DevelBoard/eva/Drawing/shield_display_4.3/shield_display_4.3.PDF

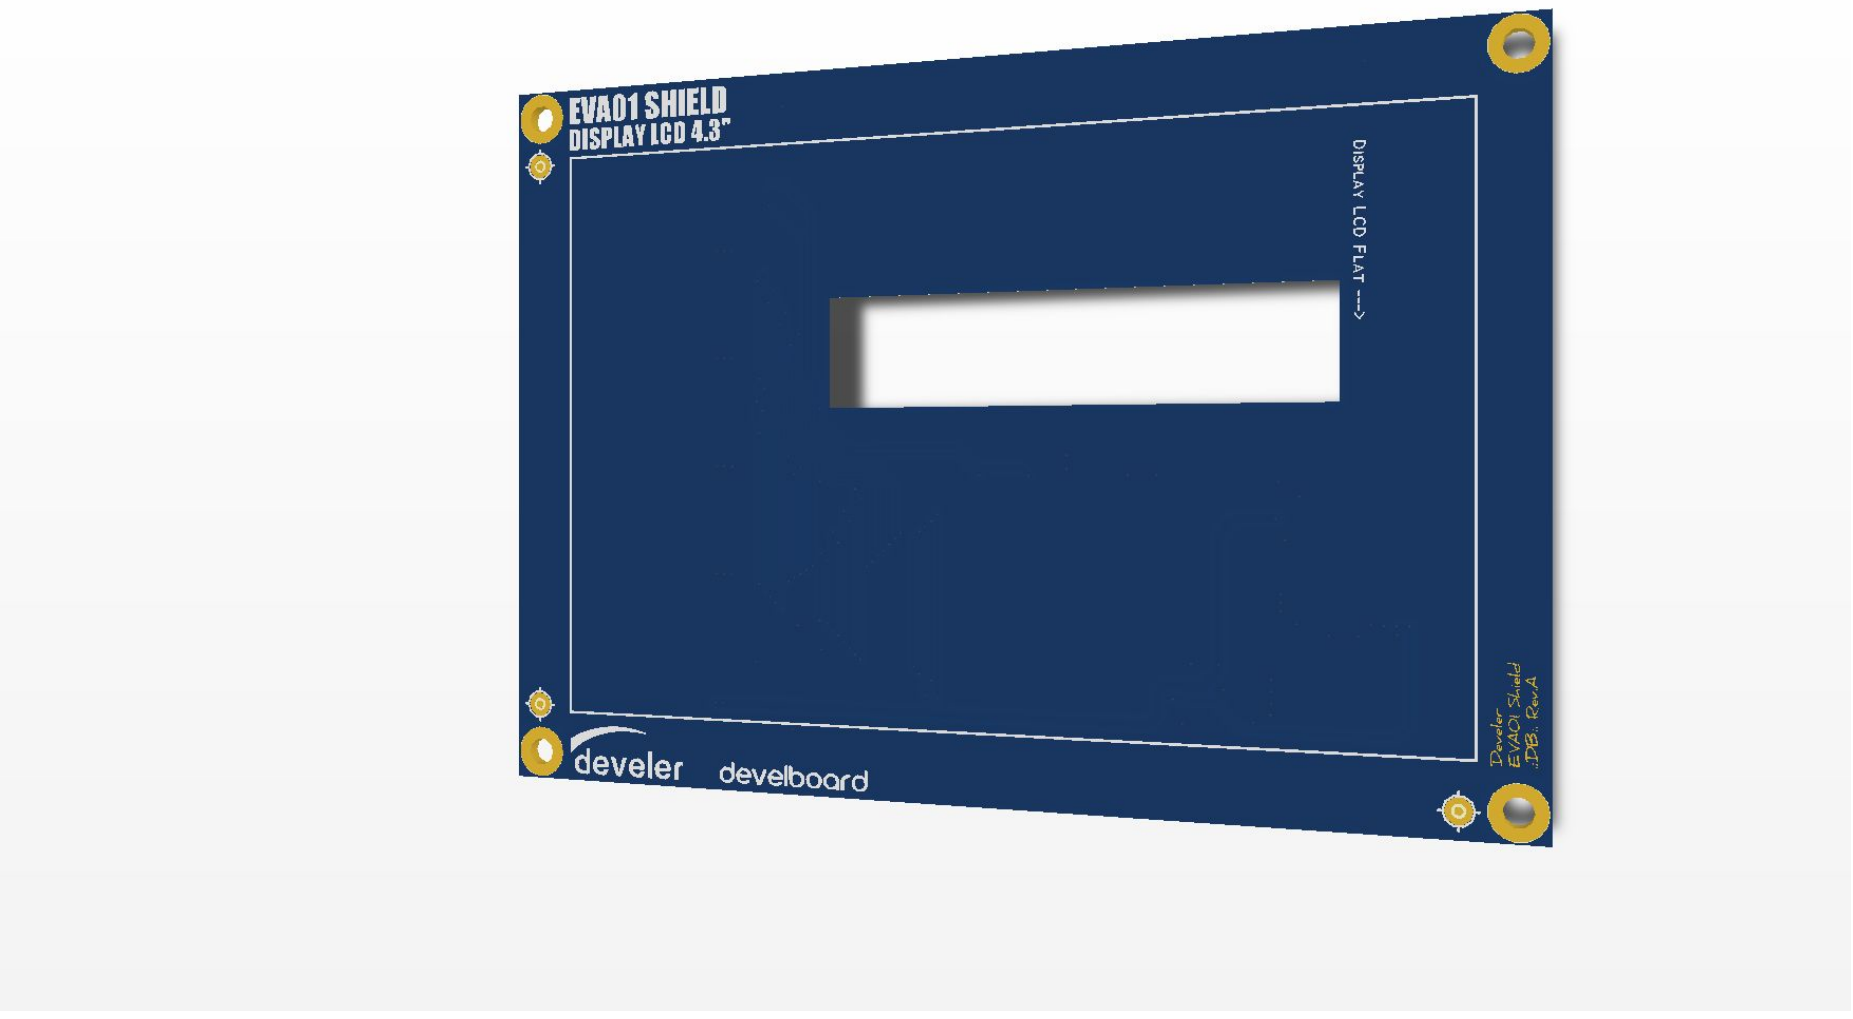
[picture p54: page 1]

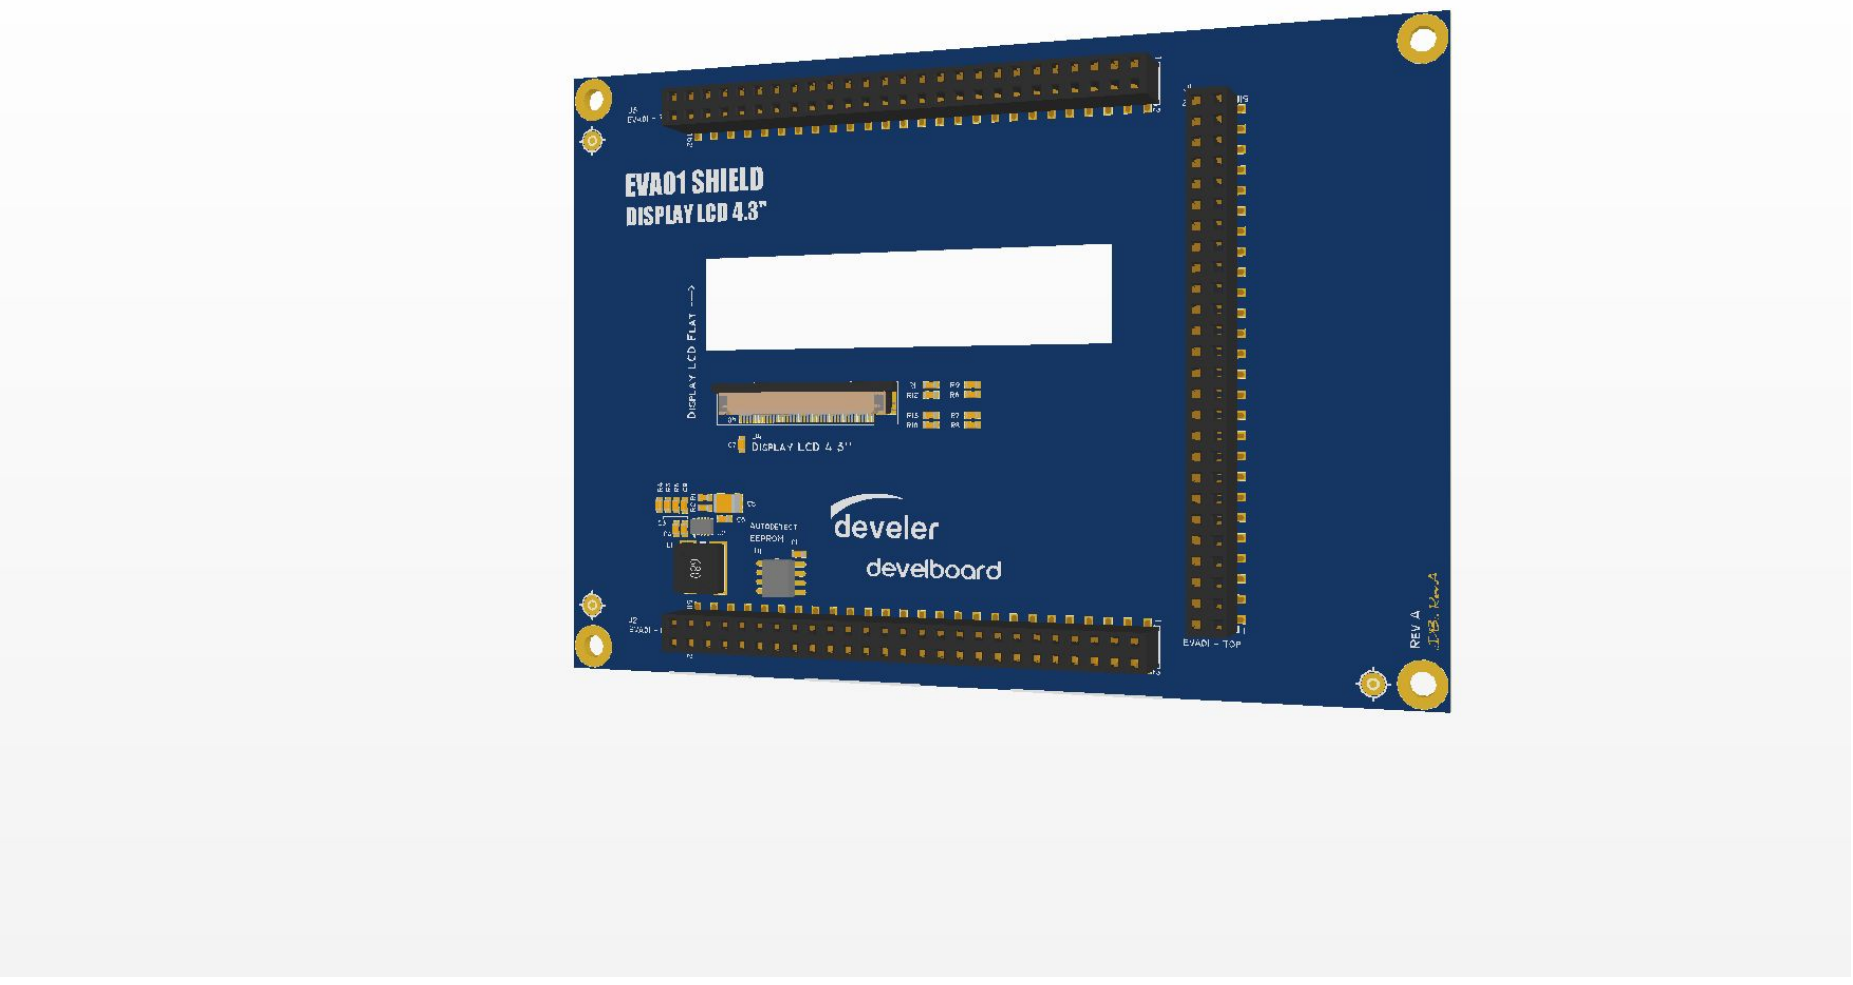
[picture p55: page 2]
