DevelBoard/eva/Drawing/shield_can-display/shield_can-display.PDF

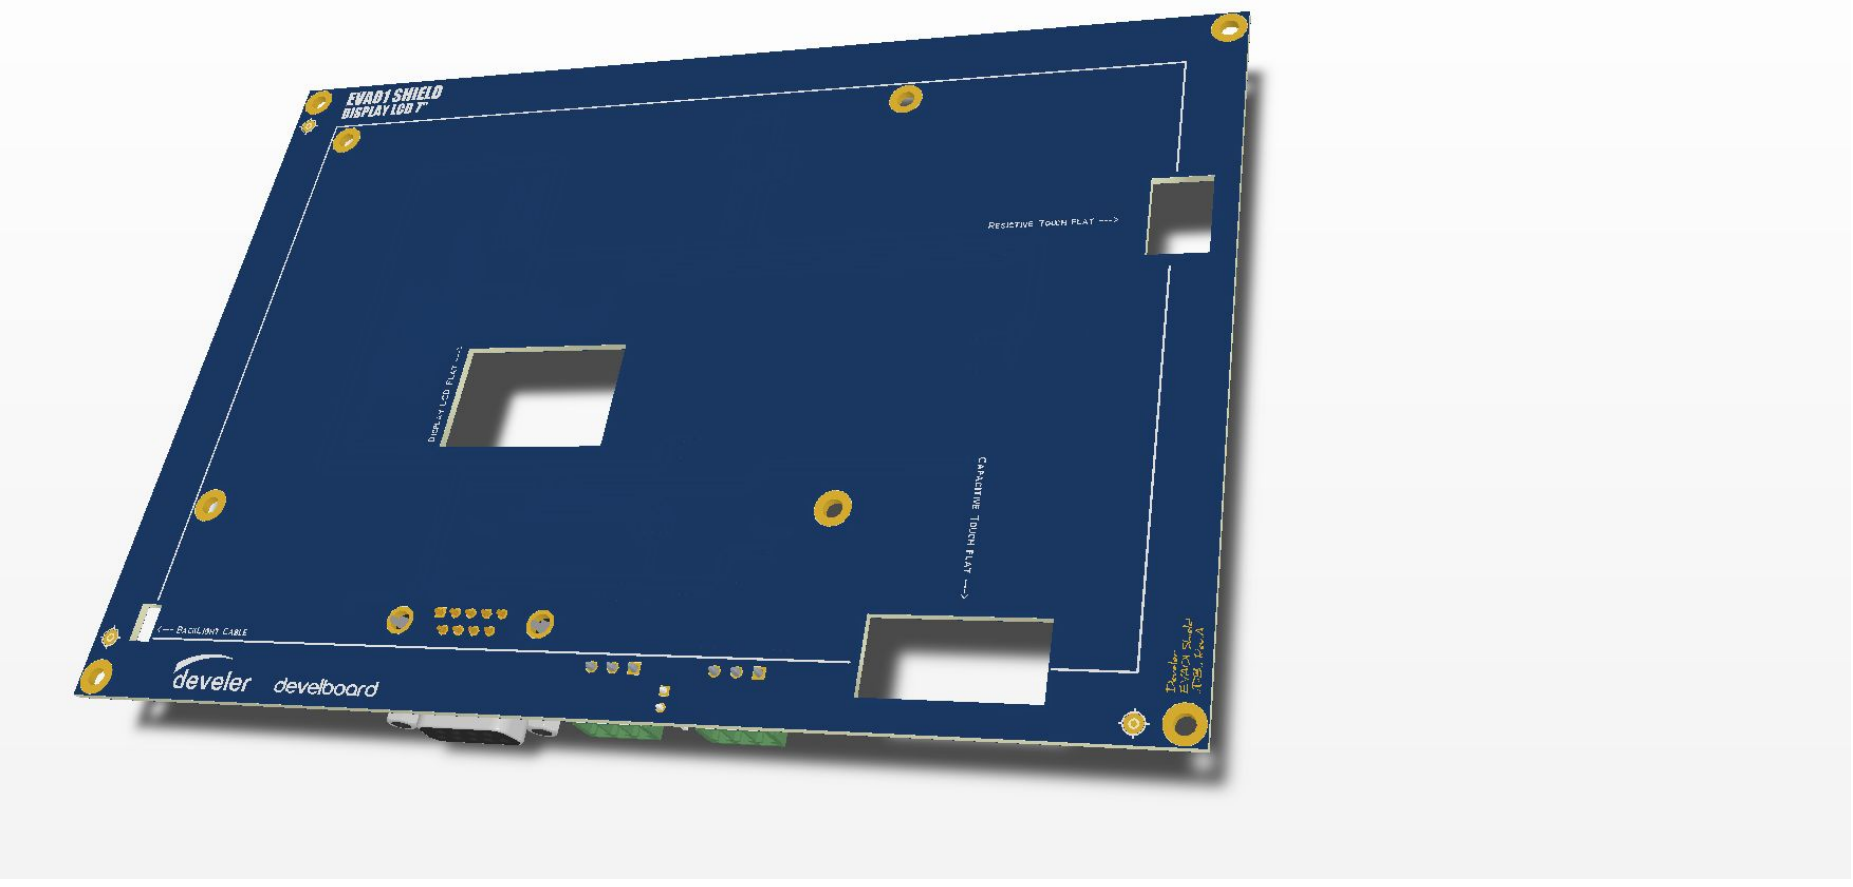
[picture p56: page 1]

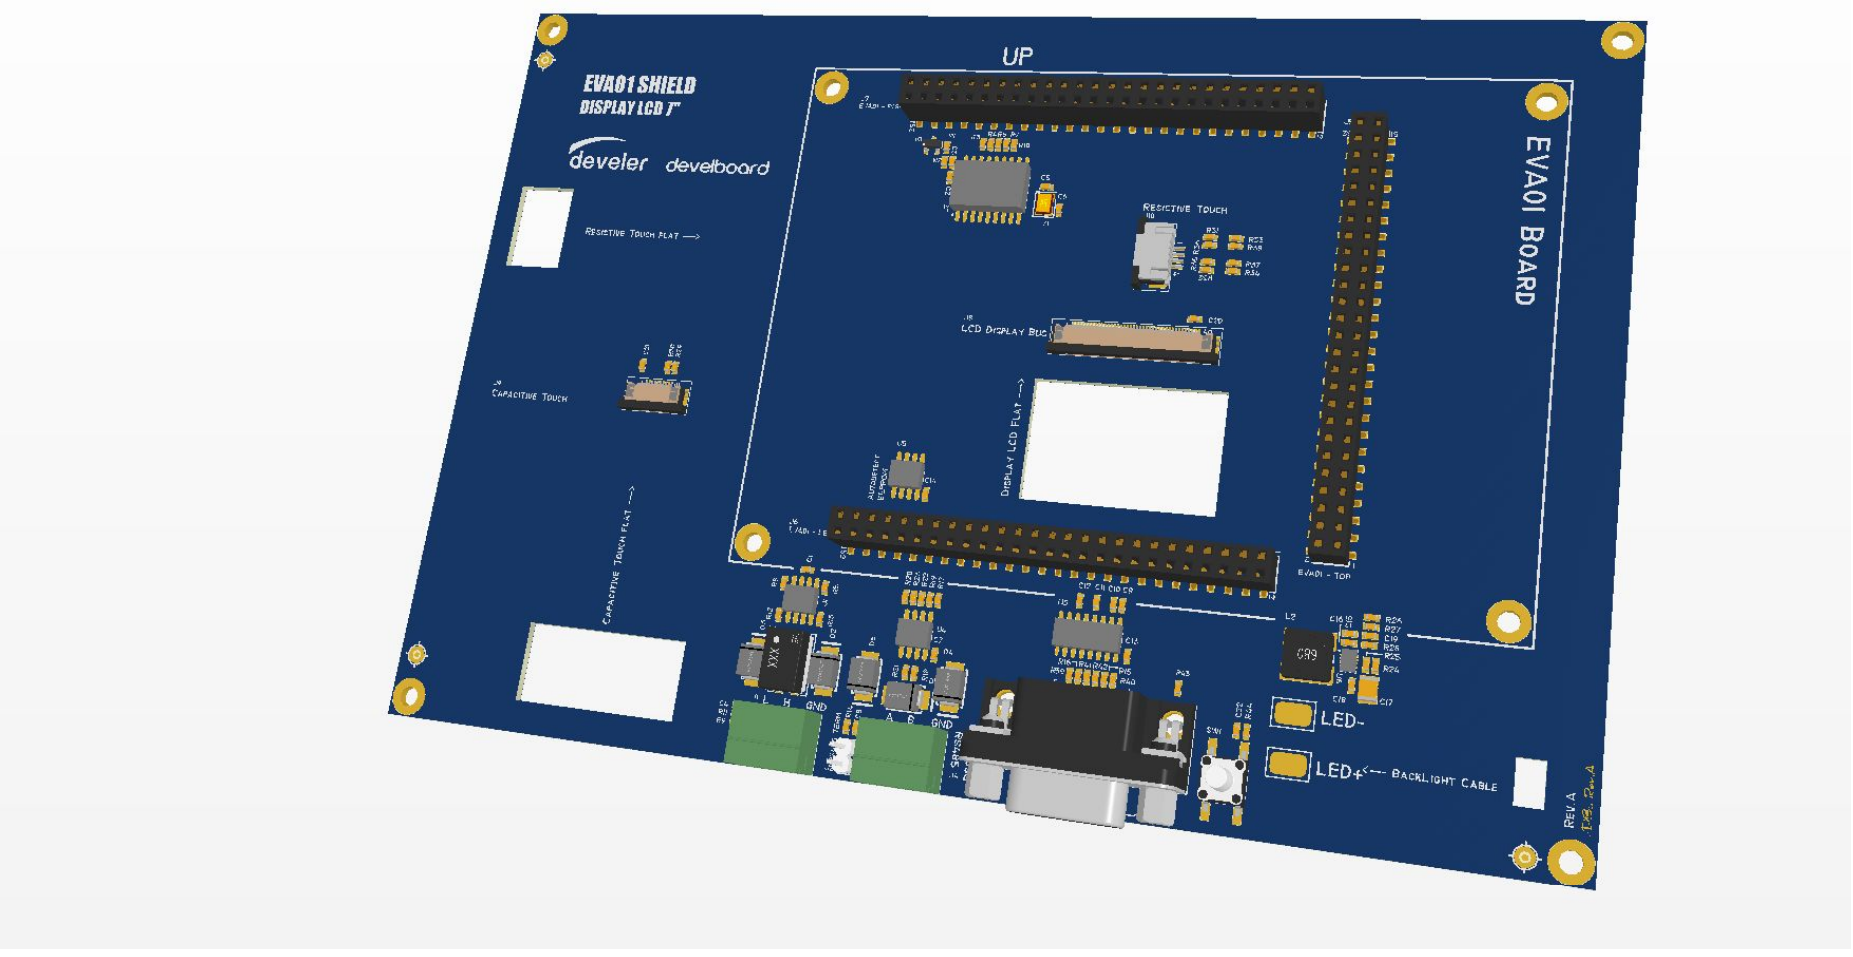
[picture p57: page 2]
