DevelBoard/eva/Drawing/eva01/develboard_eva_3d.PDF

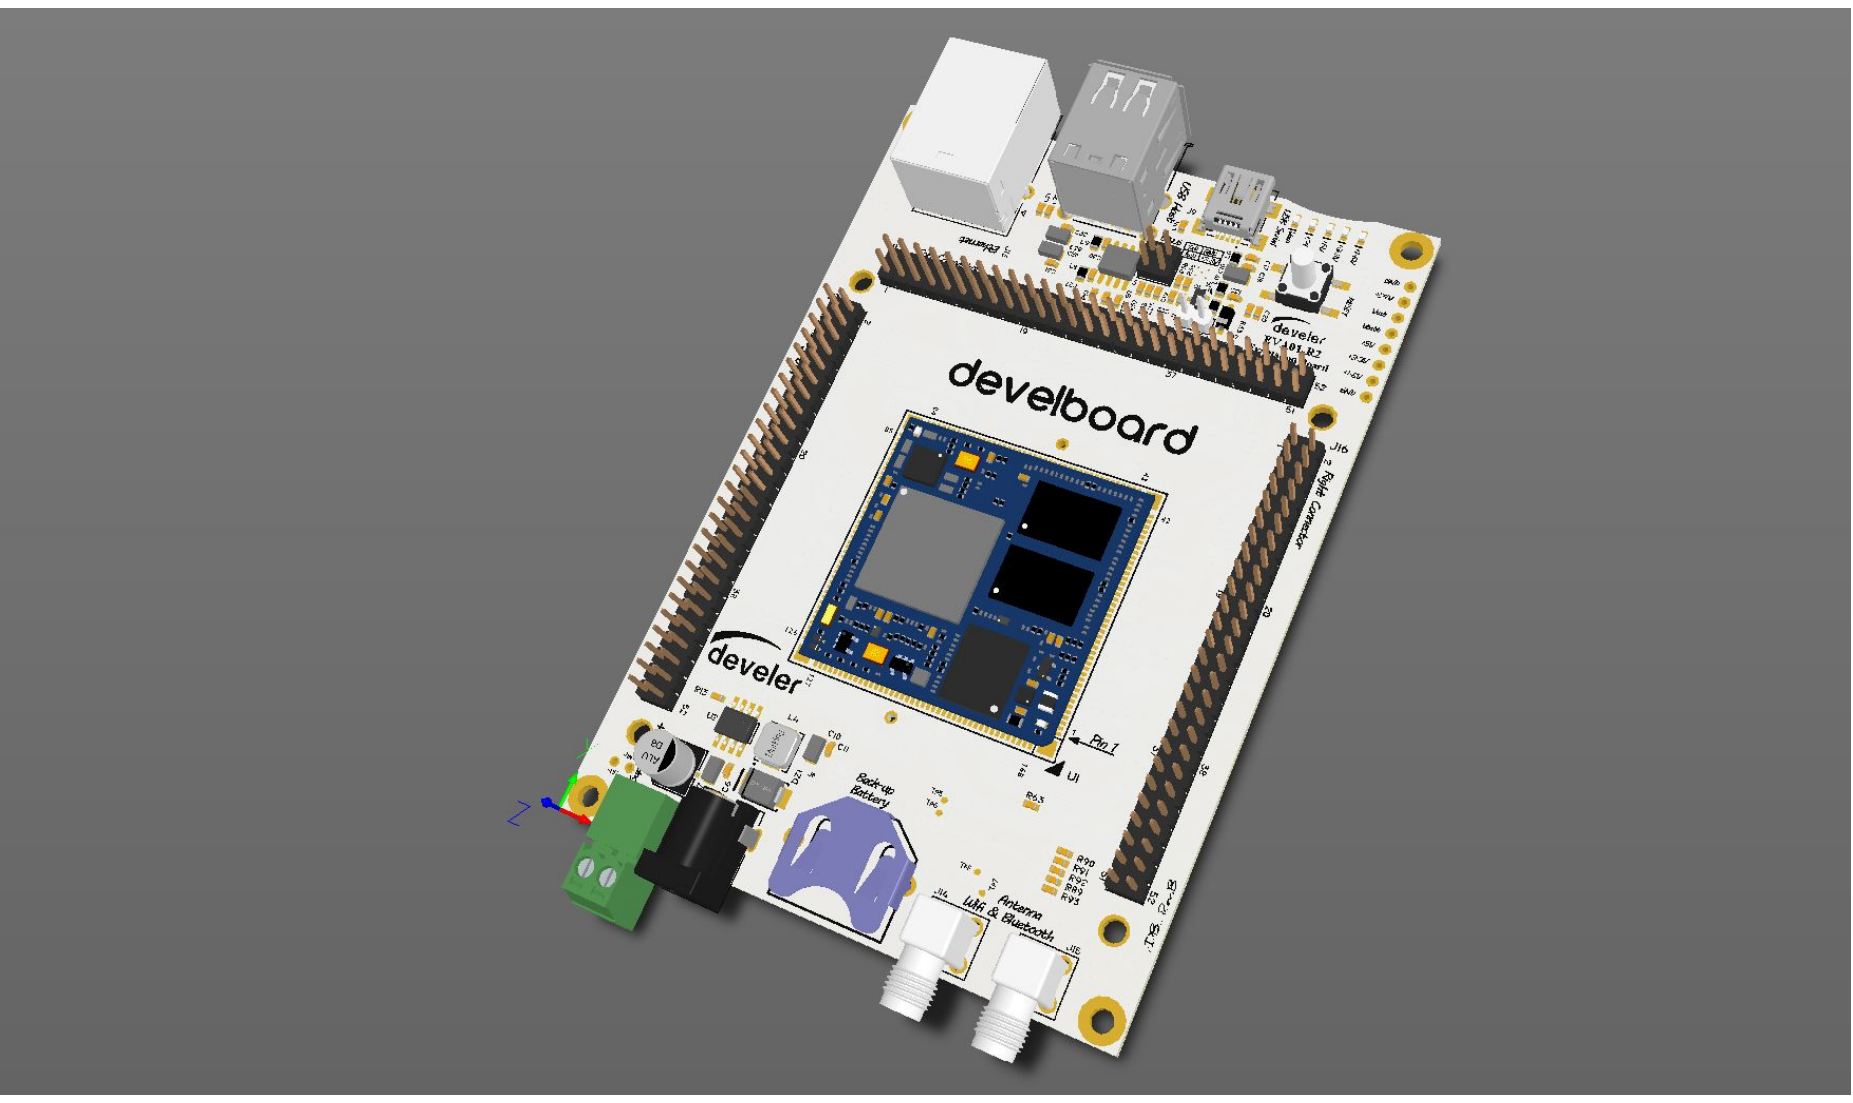
[picture p58: page 1]

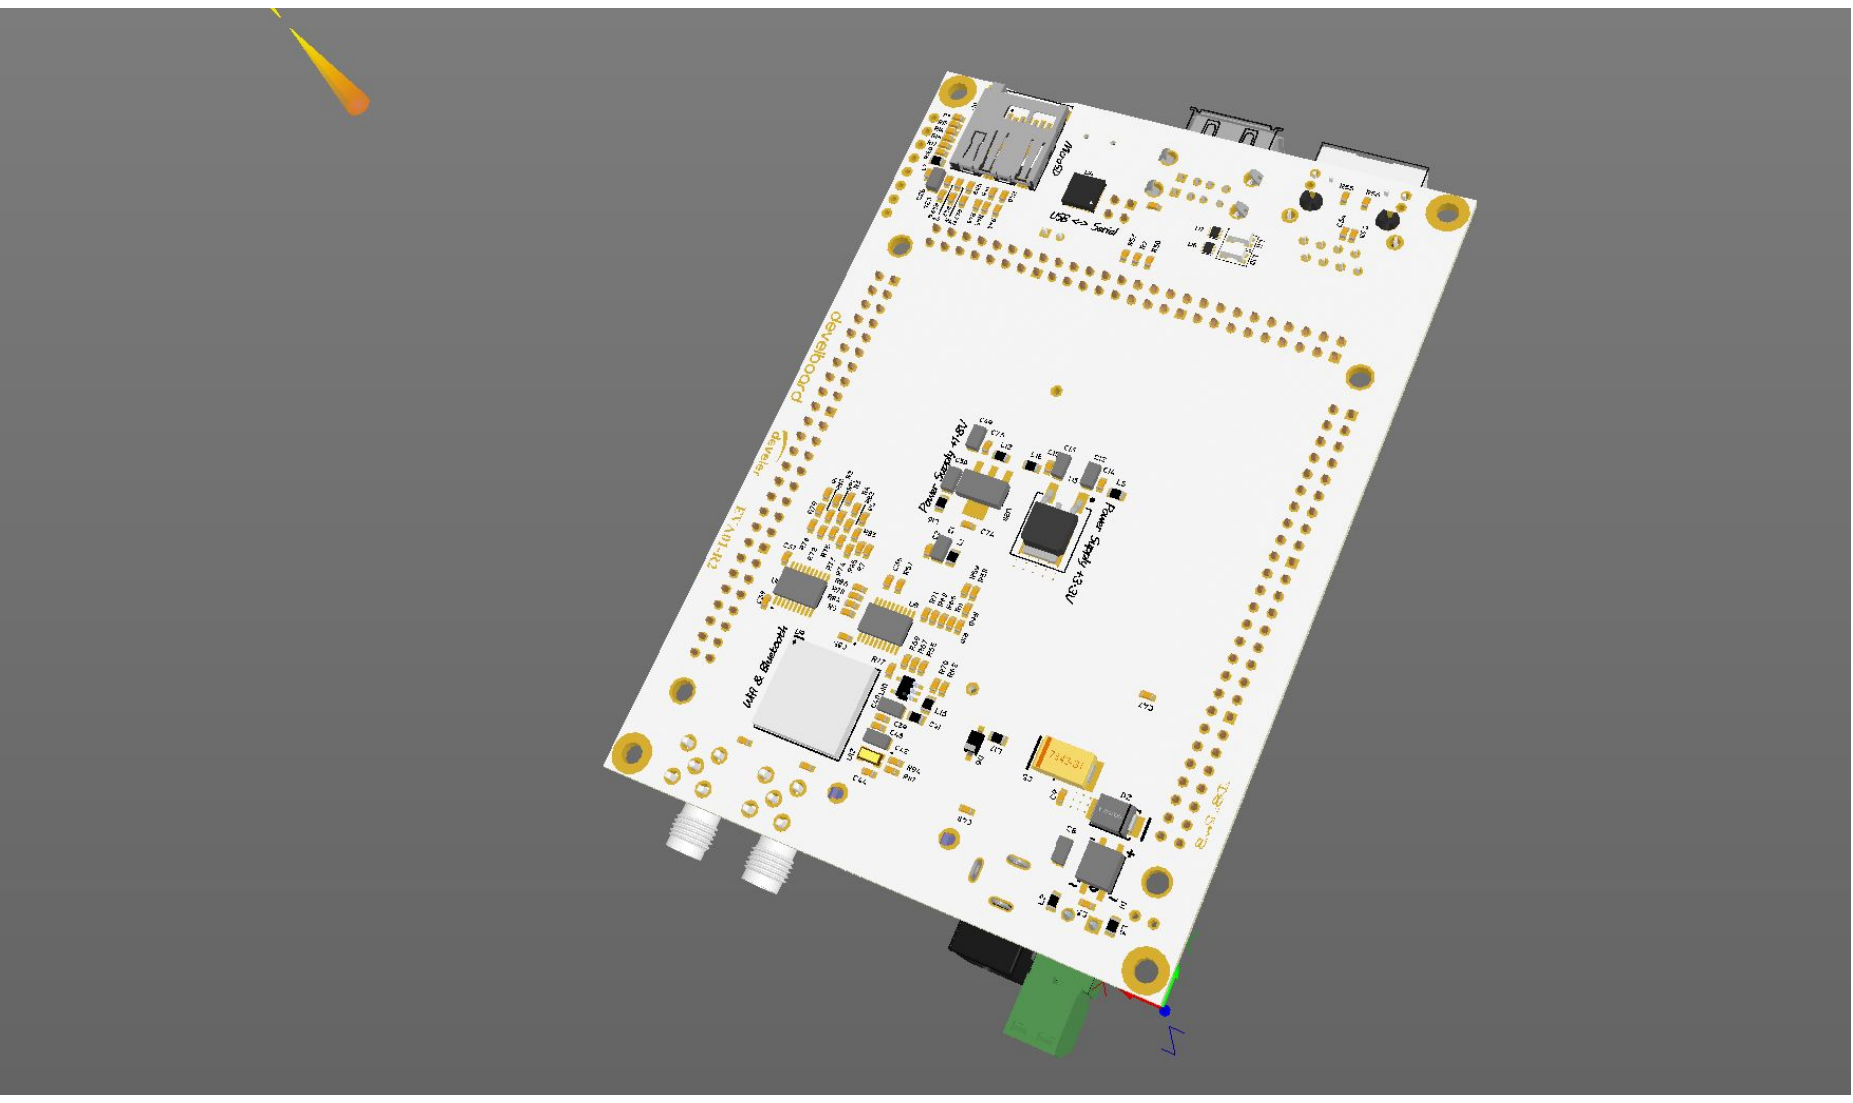
[picture p59: page 2]
